martonmiklos/boostech_l_line_bms_protocol/lline_interface/ditchedboard.jpg

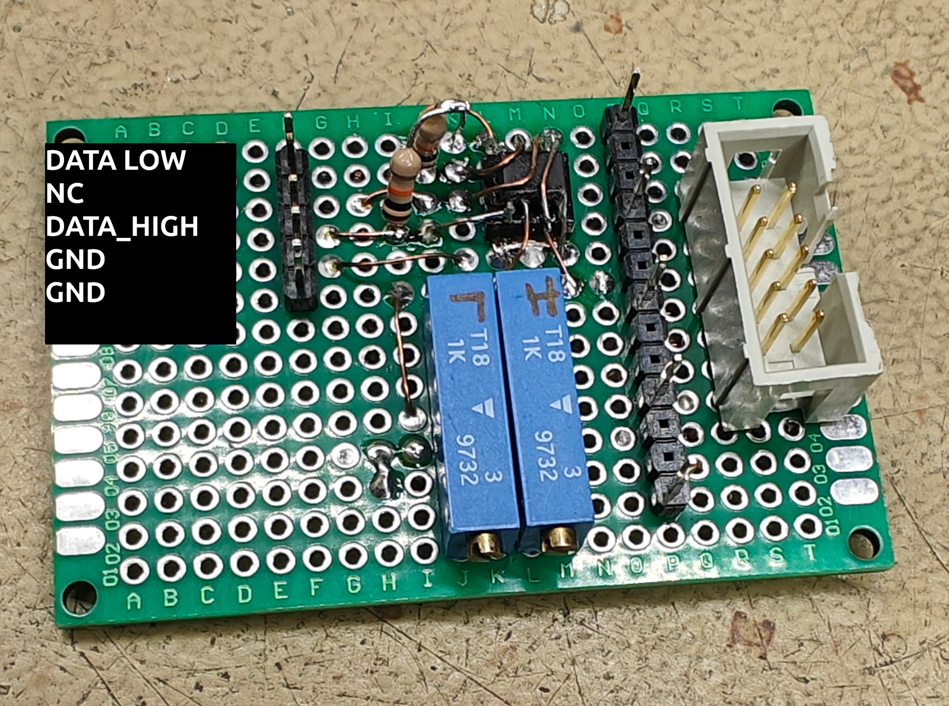
lline_interface/ditchedboard.jpg
