martonmiklos/boostech_l_line_bms_protocol/lline_interface/boostech bms.kicad_sch

## KiCad design lline_interface/boostech bms.kicad_sch (2025-07-17)

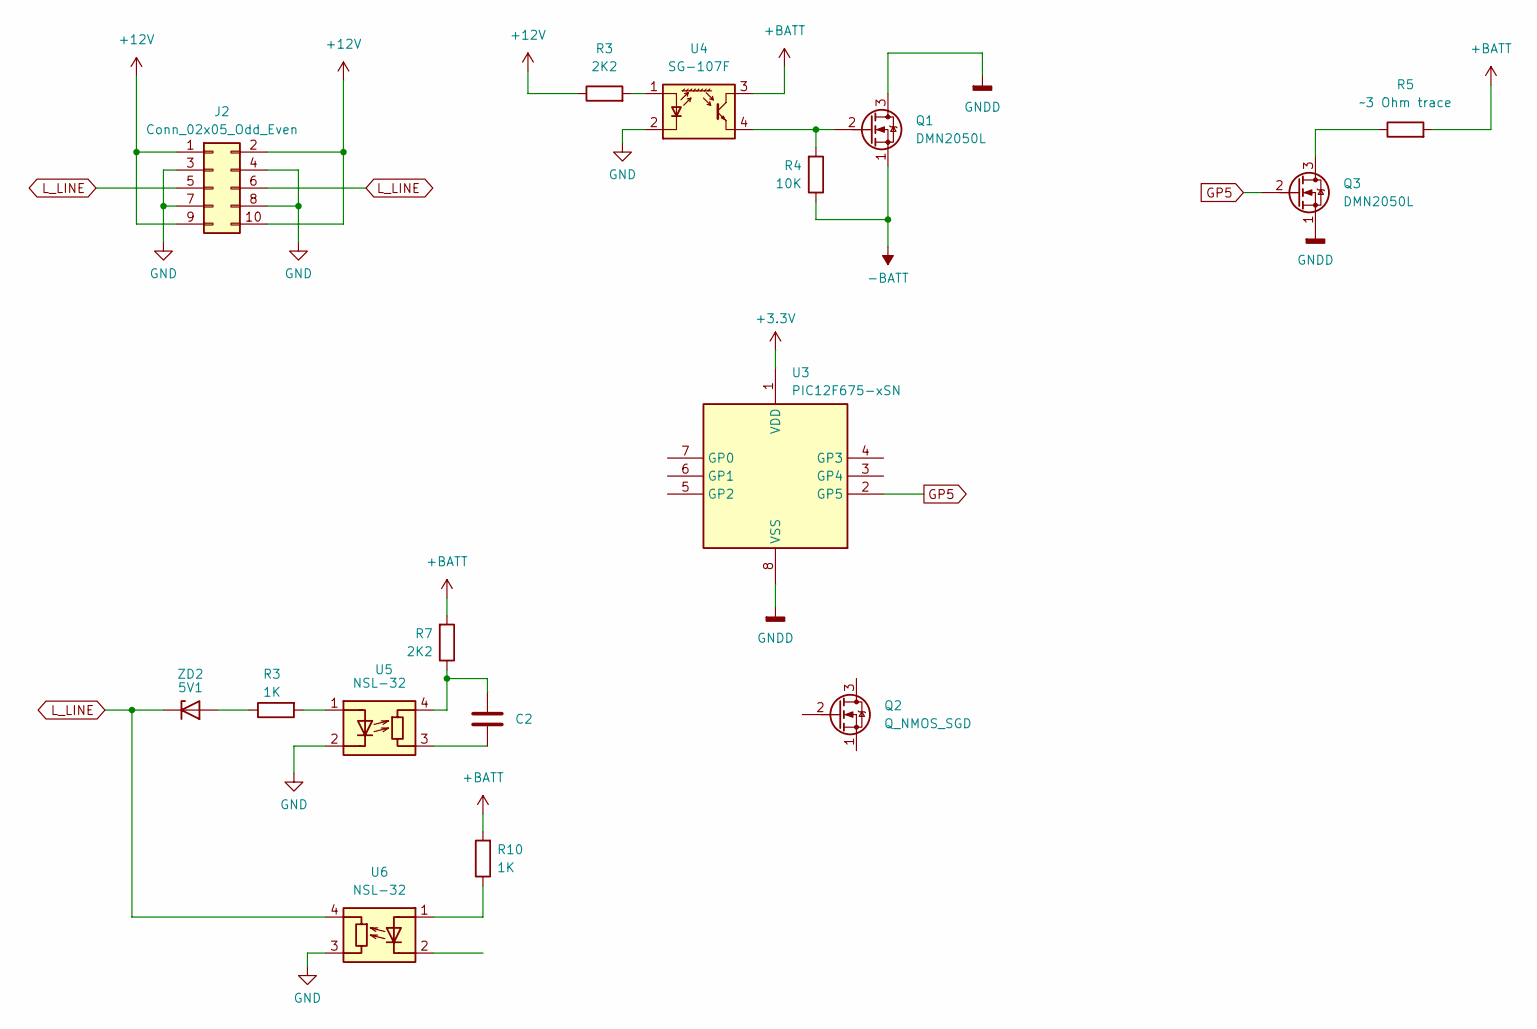
[picture p18: schematic boostech bms.kicad_sch]

Parts:
C2: C
J2: Conn_02x05_Odd_Even
Q1, Q3: DMN2050L
Q2: Q_NMOS_SGD
R3, R10: 1K
R4: 10K
R5: ~3 Ohm trace
R7: 2K2
U3: PIC12F675-xSN; SOIC-8_3.9x4.9mm_P1.27mm
U4: SG-107F; Kodenshi_SG105F
U5, U6: NSL-32; Luna_NSL-32
ZD2: 5V1

Connections:
+3.3V: U3.1 (VDD)
+12V: J2.1, J2.2, J2.9, J2.10, R3.1
+BATT: R5.2, R7.2, R10.2, U4.3 (C)
-BATT: Q1.1 (S), R4.1
GND: J2.3, J2.4, J2.7, J2.8, U4.2 (K), U5.2 (K), U6.3 (R)
GNDD: Q1.3 (D), Q3.1 (S), U3.8 (VSS)
GP5: Q3.2 (G), U3.2 (GP5)
L_LINE: J2.5, J2.6, U6.4 (R), ZD2.1 (K)
unnamed: C2.1, R7.1, U5.4 (R)
unnamed: C2.2, U5.3 (R)
unnamed: Q1.2 (G), R4.2, U4.4 (E)
unnamed: Q3.3 (D), R5.1
unnamed: R3.1, ZD2.2 (A)
unnamed: R3.2, U4.1 (A), U5.1 (A)
unnamed: R10.1, U6.1 (A)
