martonmiklos/boostech_l_line_bms_protocol/lline_interface/lline_interface.kicad_sch

## KiCad design lline_interface/lline_interface.kicad_sch (2025-07-17)

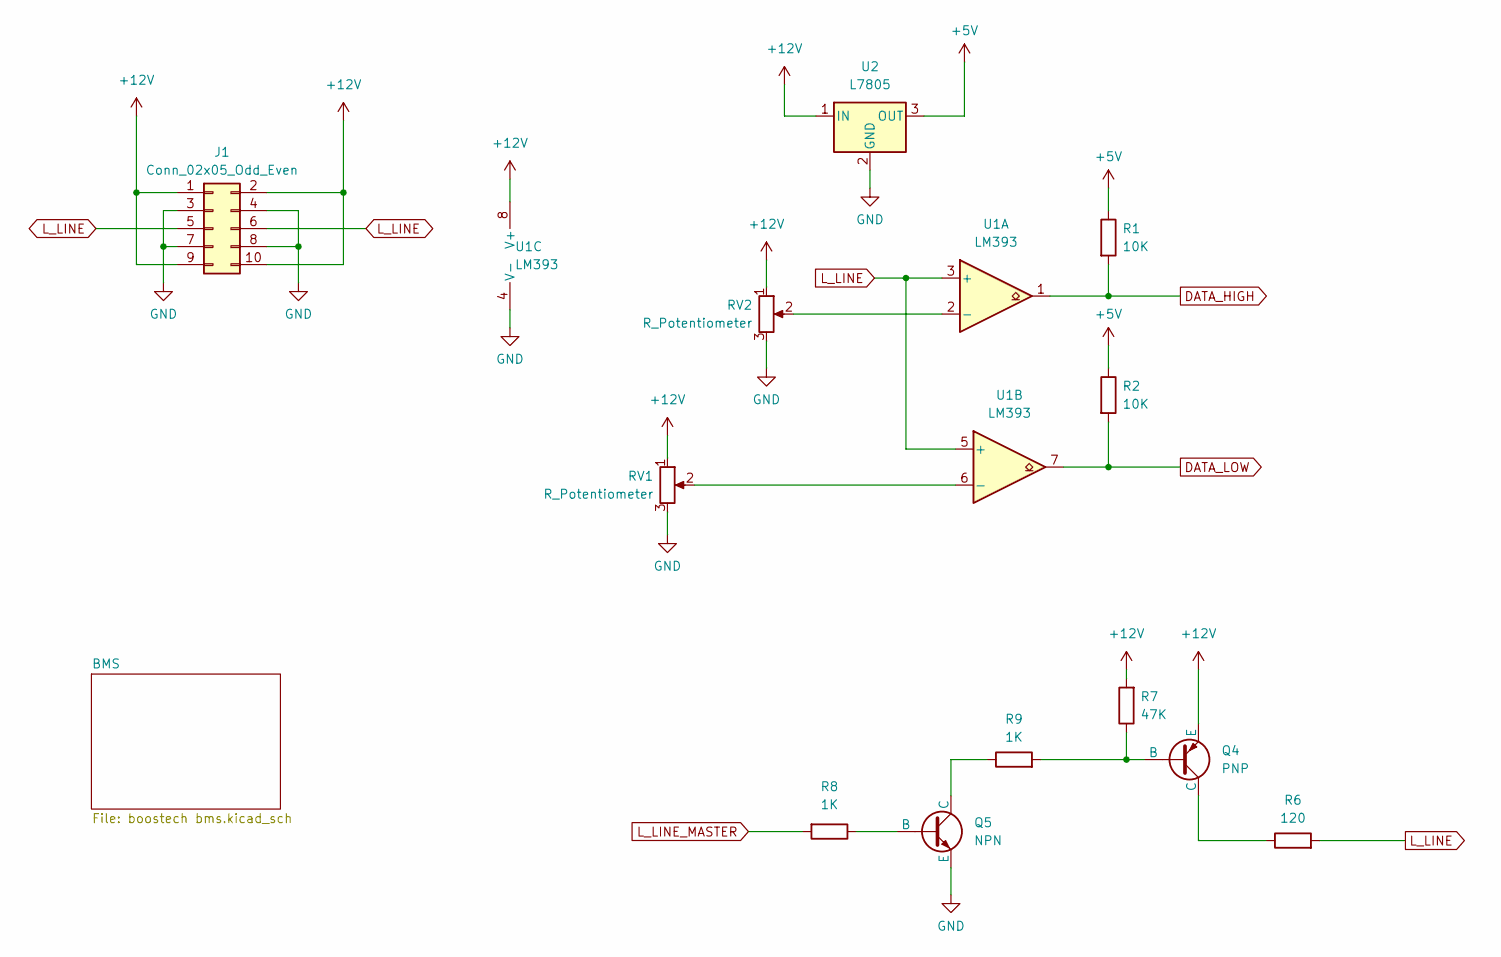
[picture p19: schematic lline_interface.kicad_sch]

Parts:
J1: Conn_02x05_Odd_Even
Q4: PNP
Q5: NPN
R1, R2: 10K
R6: 120
R7: 47K
R8, R9: 1K
RV1, RV2: R_Potentiometer
U1: LM393
U2: L7805

Connections:
+5V: R1.1, R2.1, U2.3 (OUT)
+12V: J1.1, J1.2, J1.9, J1.10, Q4.3 (E), R7.2, RV1.1, RV2.1, U1.8 (V+), U2.1 (IN)
DATA_HIGH: R1.2, U1.1
DATA_LOW: R2.2, U1.7
GND: J1.3, J1.4, J1.7, J1.8, Q5.3 (E), RV1.3, RV2.3, U1.4 (V-), U2.2 (GND)
L_LINE: J1.5, J1.6, R6.2, U1.3 (+), U1.5 (+)
L_LINE_MASTER: R8.2
unnamed: Q4.1 (C), R6.1
unnamed: Q4.2 (B), R7.1, R9.2
unnamed: Q5.1 (C), R9.1
unnamed: Q5.2 (B), R8.1
unnamed: RV1.2, U1.6 (-)
unnamed: RV2.2, U1.2 (-)
